Aahil78/KB75/src/KB75.kicad_sch

## KiCad design src/KB75.kicad_sch (2025-06-21, an earlier design)

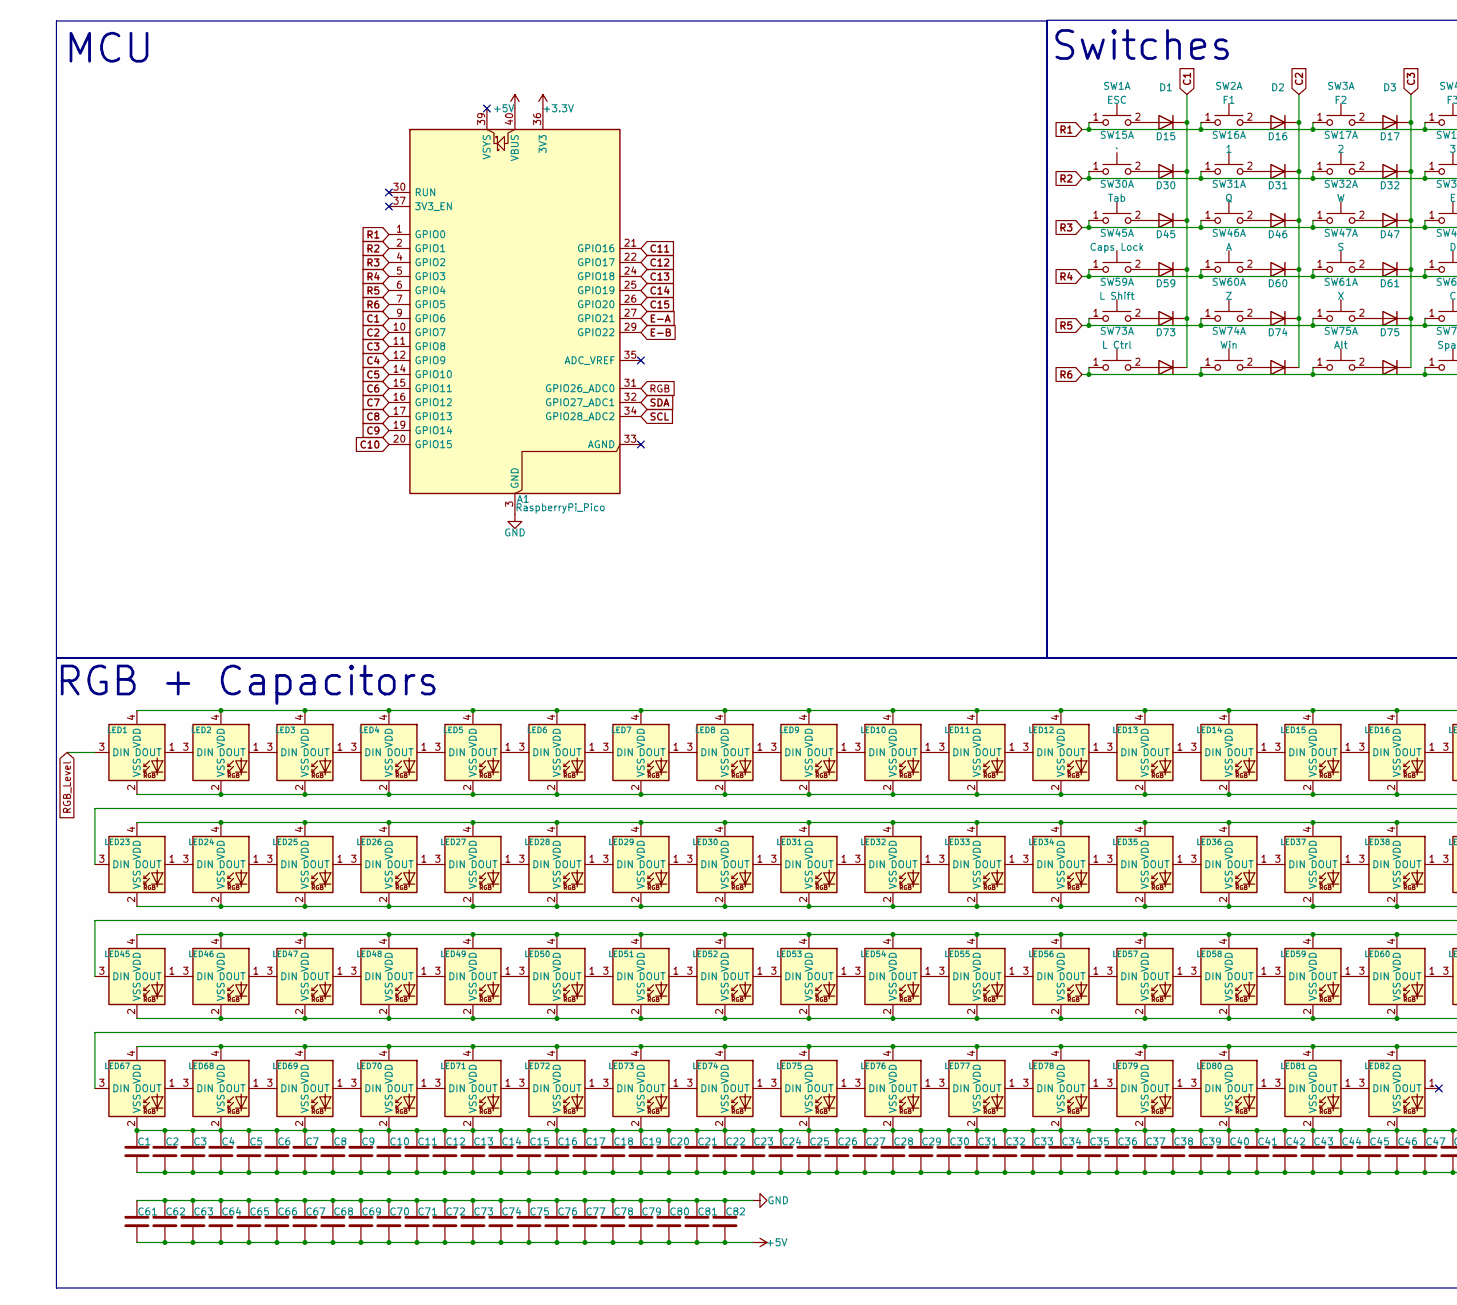
[picture p9: schematic KB75.kicad_sch, part in row 1, column 1]

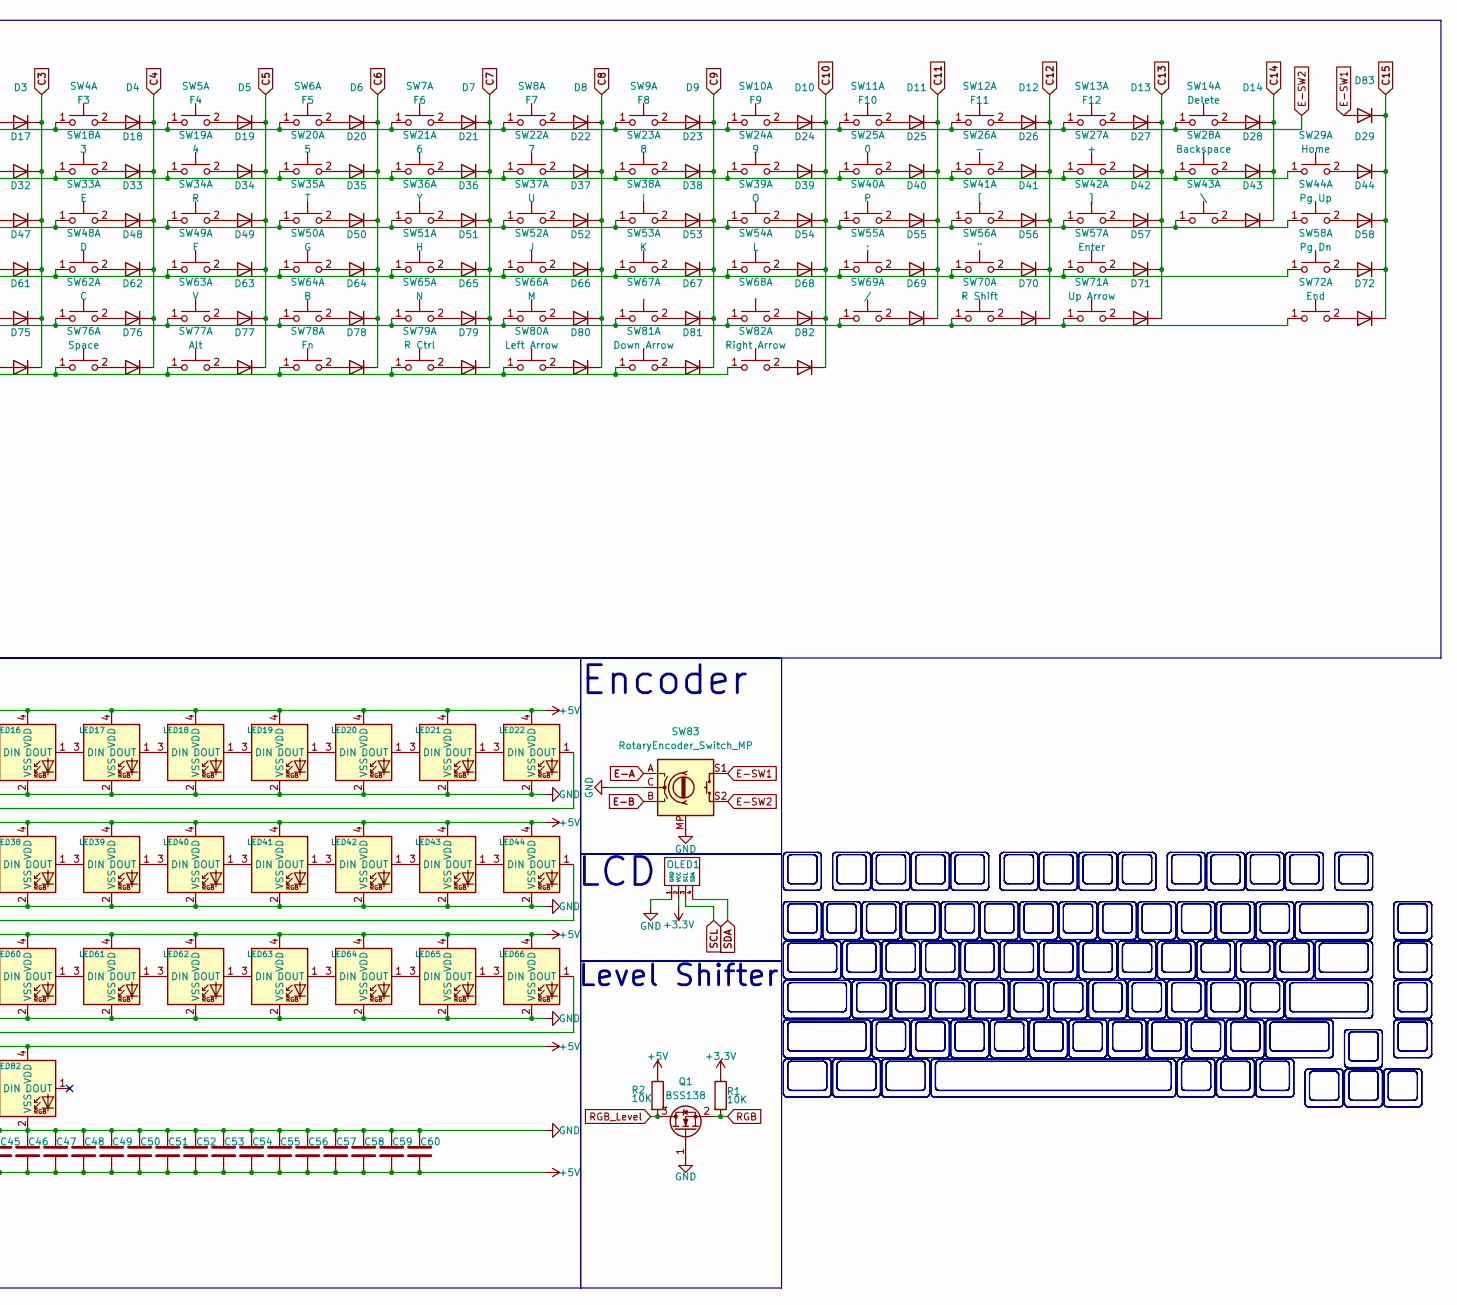
[picture p10: schematic KB75.kicad_sch, part in row 1, column 2]

Parts:
A1: RaspberryPi_Pico; RaspberryPi_Pico_Common_Unspecified
C1, C2, C3, C4, C5, C6, C7, C8, C9, C10, C11, C12, C13, C14, C15, C16, C17, C18, C19, C20, C21, C22, C23, C24, C25, C26, C27, C28, C29, C30, C31, C32, C33, C34, C35, C36, C37, C38, C39, C40, C41, C42, C43, C44, C45, C46, C47, C48, C49, C50, C51, C52, C53, C54, C55, C56, C57, C58, C59, C60, C61, C62, C63, C64, C65, C66, C67, C68, C69, C70, C71, C72, C73, C74, C75, C76, C77, C78, C79, C80, C81, C82: C; C_0805_2012Metric_Pad1.18x1.45mm_HandSolder
D1, D2, D3, D4, D5, D6, D7, D8, D9, D10, D11, D12, D13, D14, D15, D16, D17, D18, D19, D20, D21, D22, D23, D24, D25, D26, D27, D28, D29, D30, D31, D32, D33, D34, D35, D36, D37, D38, D39, D40, D41, D42, D43, D44, D45, D46, D47, D48, D49, D50, D51, D52, D53, D54, D55, D56, D57, D58, D59, D60, D61, D62, D63, D64, D65, D66, D67, D68, D69, D70, D71, D72, D73, D74, D75, D76, D77, D78, D79, D80, D81, D82, D83: D; D_0805_2012Metric_Pad1.15x1.40mm_HandSolder
LED1, LED2, LED3, LED4, LED5, LED6, LED7, LED8, LED9, LED10, LED11, LED12, LED13, LED14, LED15, LED16, LED17, LED18, LED19, LED20, LED21, LED22, LED23, LED24, LED25, LED26, LED27, LED28, LED29, LED30, LED31, LED32, LED33, LED34, LED35, LED36, LED37, LED38, LED39, LED40, LED41, LED42, LED43, LED44, LED45, LED46, LED47, LED48, LED49, LED50, LED51, LED52, LED53, LED54, LED55, LED56, LED57, LED58, LED59, LED60, LED61, LED62, LED63, LED64, LED65, LED66, LED67, LED68, LED69, LED70, LED71, LED72, LED73, LED74, LED75, LED76, LED77, LED78, LED79, LED80, LED81, LED82: MX_SK6812MINI-E
OLED1: SSD1306-0.91-OLED-4pin-128x32
Q1: BSS138; SOT-23
R1, R2: 10K; R_0805_2012Metric_Pad1.20x1.40mm_HandSolder
SW1: ESC; SW_Hotswap_Kailh_MX_1.00u
SW2: F1; SW_Hotswap_Kailh_MX_1.00u
SW3: F2; SW_Hotswap_Kailh_MX_1.00u
SW4: F3; SW_Hotswap_Kailh_MX_1.00u
SW5: F4; SW_Hotswap_Kailh_MX_1.00u
SW6: F5; SW_Hotswap_Kailh_MX_1.00u
SW7: F6; SW_Hotswap_Kailh_MX_1.00u
SW8: F7; SW_Hotswap_Kailh_MX_1.00u
SW9: F8; SW_Hotswap_Kailh_MX_1.00u
SW10: F9; SW_Hotswap_Kailh_MX_1.00u
SW11: F10; SW_Hotswap_Kailh_MX_1.00u
SW12: F11; SW_Hotswap_Kailh_MX_1.00u
SW13: F12; SW_Hotswap_Kailh_MX_1.00u
SW14: Delete; SW_Hotswap_Kailh_MX_1.00u
SW15: `; SW_Hotswap_Kailh_MX_1.00u
SW16: 1; SW_Hotswap_Kailh_MX_1.00u
SW17: 2; SW_Hotswap_Kailh_MX_1.00u
SW18: 3; SW_Hotswap_Kailh_MX_1.00u
SW19: 4; SW_Hotswap_Kailh_MX_1.00u
SW20: 5; SW_Hotswap_Kailh_MX_1.00u
SW21: 6; SW_Hotswap_Kailh_MX_1.00u
SW22: 7; SW_Hotswap_Kailh_MX_1.00u
SW23: 8; SW_Hotswap_Kailh_MX_1.00u
SW24: 9; SW_Hotswap_Kailh_MX_1.00u
SW25: 0; SW_Hotswap_Kailh_MX_1.00u
SW26: -; SW_Hotswap_Kailh_MX_1.00u
SW27: +; SW_Hotswap_Kailh_MX_1.00u
SW28: Backspace; SW_Hotswap_Kailh_MX_1.00u
SW29: Home; SW_Hotswap_Kailh_MX_1.00u
SW30: Tab; SW_Hotswap_Kailh_MX_1.00u
SW31: Q; SW_Hotswap_Kailh_MX_1.00u
SW32: W; SW_Hotswap_Kailh_MX_1.00u
SW33: E; SW_Hotswap_Kailh_MX_1.00u
SW34: R; SW_Hotswap_Kailh_MX_1.00u
SW35: T; SW_Hotswap_Kailh_MX_1.00u
SW36: Y; SW_Hotswap_Kailh_MX_1.00u
SW37: U; SW_Hotswap_Kailh_MX_1.00u
SW38: I; SW_Hotswap_Kailh_MX_1.00u
SW39: O; SW_Hotswap_Kailh_MX_1.00u
SW40: P; SW_Hotswap_Kailh_MX_1.00u
SW41: [; SW_Hotswap_Kailh_MX_1.00u
SW42: ]; SW_Hotswap_Kailh_MX_1.00u
SW43: \; SW_Hotswap_Kailh_MX_1.00u
SW44: Pg Up; SW_Hotswap_Kailh_MX_1.00u
SW45: Caps Lock; SW_Hotswap_Kailh_MX_1.00u
SW46: A; SW_Hotswap_Kailh_MX_1.00u
SW47: S; SW_Hotswap_Kailh_MX_1.00u
SW48: D; SW_Hotswap_Kailh_MX_1.00u
SW49: F; SW_Hotswap_Kailh_MX_1.00u
SW50: G; SW_Hotswap_Kailh_MX_1.00u
SW51: H; SW_Hotswap_Kailh_MX_1.00u
SW52: J; SW_Hotswap_Kailh_MX_1.00u
SW53: K; SW_Hotswap_Kailh_MX_1.00u
SW54: L; SW_Hotswap_Kailh_MX_1.00u
SW55: ;; SW_Hotswap_Kailh_MX_1.00u
SW56: "; SW_Hotswap_Kailh_MX_1.00u
SW57: Enter; SW_Hotswap_Kailh_MX_1.00u
SW58: Pg Dn; SW_Hotswap_Kailh_MX_1.00u
SW59: L Shift; SW_Hotswap_Kailh_MX_1.00u
SW60: Z; SW_Hotswap_Kailh_MX_1.00u
SW61: X; SW_Hotswap_Kailh_MX_1.00u
SW62: C; SW_Hotswap_Kailh_MX_1.00u
SW63: V; SW_Hotswap_Kailh_MX_1.00u
SW64: B; SW_Hotswap_Kailh_MX_1.00u
SW65: N; SW_Hotswap_Kailh_MX_1.00u
SW66: M; SW_Hotswap_Kailh_MX_1.00u
SW67: ,; SW_Hotswap_Kailh_MX_1.00u
SW68: .; SW_Hotswap_Kailh_MX_1.00u
SW69: /; SW_Hotswap_Kailh_MX_1.00u
SW70: R Shift; SW_Hotswap_Kailh_MX_1.00u
SW71: Up Arrow; SW_Hotswap_Kailh_MX_1.00u
SW72: End; SW_Hotswap_Kailh_MX_1.00u
SW73: L Ctrl; SW_Hotswap_Kailh_MX_1.00u
SW74: Win; SW_Hotswap_Kailh_MX_1.00u
SW75, SW77: Alt; SW_Hotswap_Kailh_MX_1.00u
SW76: Space; SW_Hotswap_Kailh_MX_1.00u
SW78: Fn; SW_Hotswap_Kailh_MX_1.00u
SW79: R Ctrl; SW_Hotswap_Kailh_MX_1.00u
SW80: Left Arrow; SW_Hotswap_Kailh_MX_1.00u
SW81: Down Arrow; SW_Hotswap_Kailh_MX_1.00u
SW82: Right Arrow; SW_Hotswap_Kailh_MX_1.00u
SW83: RotaryEncoder_Switch_MP; RotaryEncoder_Alps_EC11E-Switch_Vertical_H20mm

Connections:
+3.3V: A1.36 (3V3), OLED1.2 (VCC), R1.1
+5V: A1.40 (VBUS), C1.2, C2.2, C3.2, C4.2, C5.2, C6.2, C7.2, C8.2, C9.2, C10.2, C11.2, C12.2, C13.2, C14.2, C15.2, C16.2, C17.2, C18.2, C19.2, C20.2, C21.2, C22.2, C23.2, C24.2, C25.2, C26.2, C27.2, C28.2, C29.2, C30.2, C31.2, C32.2, C33.2, C34.2, C35.2, C36.2, C37.2, C38.2, C39.2, C40.2, C41.2, C42.2, C43.2, C44.2, C45.2, C46.2, C47.2, C48.2, C49.2, C50.2, C51.2, C52.2, C53.2, C54.2, C55.2, C56.2, C57.2, C58.2, C59.2, C60.2, C61.2, C62.2, C63.2, C64.2, C65.2, C66.2, C67.2, C68.2, C69.2, C70.2, C71.2, C72.2, C73.2, C74.2, C75.2, C76.2, C77.2, C78.2, C79.2, C80.2, C81.2, C82.2, LED1.4 (VDD), LED2.4 (VDD), LED3.4 (VDD), LED4.4 (VDD), LED5.4 (VDD), LED6.4 (VDD), LED7.4 (VDD), LED8.4 (VDD), LED9.4 (VDD), LED10.4 (VDD), LED11.4 (VDD), LED12.4 (VDD), LED13.4 (VDD), LED14.4 (VDD), LED15.4 (VDD), LED16.4 (VDD), LED17.4 (VDD), LED18.4 (VDD), LED19.4 (VDD), LED20.4 (VDD), LED21.4 (VDD), LED22.4 (VDD), LED23.4 (VDD), LED24.4 (VDD), LED25.4 (VDD), LED26.4 (VDD), LED27.4 (VDD), LED28.4 (VDD), LED29.4 (VDD), LED30.4 (VDD), LED31.4 (VDD), LED32.4 (VDD), LED33.4 (VDD), LED34.4 (VDD), LED35.4 (VDD), LED36.4 (VDD), LED37.4 (VDD), LED38.4 (VDD), LED39.4 (VDD), LED40.4 (VDD), LED41.4 (VDD), LED42.4 (VDD), LED43.4 (VDD), LED44.4 (VDD), LED45.4 (VDD), LED46.4 (VDD), LED47.4 (VDD), LED48.4 (VDD), LED49.4 (VDD), LED50.4 (VDD), LED51.4 (VDD), LED52.4 (VDD), LED53.4 (VDD), LED54.4 (VDD), LED55.4 (VDD), LED56.4 (VDD), LED57.4 (VDD), LED58.4 (VDD), LED59.4 (VDD), LED60.4 (VDD), LED61.4 (VDD), LED62.4 (VDD), LED63.4 (VDD), LED64.4 (VDD), LED65.4 (VDD), LED66.4 (VDD), LED67.4 (VDD), LED68.4 (VDD), LED69.4 (VDD), LED70.4 (VDD), LED71.4 (VDD), LED72.4 (VDD), LED73.4 (VDD), LED74.4 (VDD), LED75.4 (VDD), LED76.4 (VDD), LED77.4 (VDD), LED78.4 (VDD), LED79.4 (VDD), LED80.4 (VDD), LED81.4 (VDD), LED82.4 (VDD), R2.1
C1: A1.9 (GPIO6), D1.1 (K), D15.1 (K), D30.1 (K), D45.1 (K), D59.1 (K), D73.1 (K)
C2: A1.10 (GPIO7), D2.1 (K), D16.1 (K), D31.1 (K), D46.1 (K), D60.1 (K), D74.1 (K)
C3: A1.11 (GPIO8), D3.1 (K), D17.1 (K), D32.1 (K), D47.1 (K), D61.1 (K), D75.1 (K)
C4: A1.12 (GPIO9), D4.1 (K), D18.1 (K), D33.1 (K), D48.1 (K), D62.1 (K), D76.1 (K)
C5: A1.14 (GPIO10), D5.1 (K), D19.1 (K), D34.1 (K), D49.1 (K), D63.1 (K), D77.1 (K)
C6: A1.15 (GPIO11), D6.1 (K), D20.1 (K), D35.1 (K), D50.1 (K), D64.1 (K), D78.1 (K)
C7: A1.16 (GPIO12), D7.1 (K), D21.1 (K), D36.1 (K), D51.1 (K), D65.1 (K), D79.1 (K)
C8: A1.17 (GPIO13), D8.1 (K), D22.1 (K), D37.1 (K), D52.1 (K), D66.1 (K), D80.1 (K)
C9: A1.19 (GPIO14), D9.1 (K), D23.1 (K), D38.1 (K), D53.1 (K), D67.1 (K), D81.1 (K)
C10: A1.20 (GPIO15), D10.1 (K), D24.1 (K), D39.1 (K), D54.1 (K), D68.1 (K), D82.1 (K)
C11: A1.21 (GPIO16), D11.1 (K), D25.1 (K), D40.1 (K), D55.1 (K), D69.1 (K)
C12: A1.22 (GPIO17), D12.1 (K), D26.1 (K), D41.1 (K), D56.1 (K), D70.1 (K)
C13: A1.24 (GPIO18), D13.1 (K), D27.1 (K), D42.1 (K), D57.1 (K), D71.1 (K)
C14: A1.25 (GPIO19), D14.1 (K), D28.1 (K), D43.1 (K)
C15: A1.26 (GPIO20), D29.1 (K), D44.1 (K), D58.1 (K), D72.1 (K), D83.1 (K)
E-A: A1.27 (GPIO21), SW83.A
E-B: A1.29 (GPIO22), SW83.B
E-SW1: D83.2 (A), SW83.S1
E-SW2: A1.1 (GPIO0), SW1.1, SW2.1, SW3.1, SW4.1, SW5.1, SW6.1, SW7.1, SW8.1, SW9.1, SW10.1, SW11.1, SW12.1, SW13.1, SW14.1, SW83.S2
GND: A1.3 (GND), A1.8 (GND), A1.13 (GND), A1.18 (GND), A1.23 (GND), A1.28 (GND), A1.38 (GND), C1.1, C2.1, C3.1, C4.1, C5.1, C6.1, C7.1, C8.1, C9.1, C10.1, C11.1, C12.1, C13.1, C14.1, C15.1, C16.1, C17.1, C18.1, C19.1, C20.1, C21.1, C22.1, C23.1, C24.1, C25.1, C26.1, C27.1, C28.1, C29.1, C30.1, C31.1, C32.1, C33.1, C34.1, C35.1, C36.1, C37.1, C38.1, C39.1, C40.1, C41.1, C42.1, C43.1, C44.1, C45.1, C46.1, C47.1, C48.1, C49.1, C50.1, C51.1, C52.1, C53.1, C54.1, C55.1, C56.1, C57.1, C58.1, C59.1, C60.1, C61.1, C62.1, C63.1, C64.1, C65.1, C66.1, C67.1, C68.1, C69.1, C70.1, C71.1, C72.1, C73.1, C74.1, C75.1, C76.1, C77.1, C78.1, C79.1, C80.1, C81.1, C82.1, LED1.2 (VSS), LED2.2 (VSS), LED3.2 (VSS), LED4.2 (VSS), LED5.2 (VSS), LED6.2 (VSS), LED7.2 (VSS), LED8.2 (VSS), LED9.2 (VSS), LED10.2 (VSS), LED11.2 (VSS), LED12.2 (VSS), LED13.2 (VSS), LED14.2 (VSS), LED15.2 (VSS), LED16.2 (VSS), LED17.2 (VSS), LED18.2 (VSS), LED19.2 (VSS), LED20.2 (VSS), LED21.2 (VSS), LED22.2 (VSS), LED23.2 (VSS), LED24.2 (VSS), LED25.2 (VSS), LED26.2 (VSS), LED27.2 (VSS), LED28.2 (VSS), LED29.2 (VSS), LED30.2 (VSS), LED31.2 (VSS), LED32.2 (VSS), LED33.2 (VSS), LED34.2 (VSS), LED35.2 (VSS), LED36.2 (VSS), LED37.2 (VSS), LED38.2 (VSS), LED39.2 (VSS), LED40.2 (VSS), LED41.2 (VSS), LED42.2 (VSS), LED43.2 (VSS), LED44.2 (VSS), LED45.2 (VSS), LED46.2 (VSS), LED47.2 (VSS), LED48.2 (VSS), LED49.2 (VSS), LED50.2 (VSS), LED51.2 (VSS), LED52.2 (VSS), LED53.2 (VSS), LED54.2 (VSS), LED55.2 (VSS), LED56.2 (VSS), LED57.2 (VSS), LED58.2 (VSS), LED59.2 (VSS), LED60.2 (VSS), LED61.2 (VSS), LED62.2 (VSS), LED63.2 (VSS), LED64.2 (VSS), LED65.2 (VSS), LED66.2 (VSS), LED67.2 (VSS), LED68.2 (VSS), LED69.2 (VSS), LED70.2 (VSS), LED71.2 (VSS), LED72.2 (VSS), LED73.2 (VSS), LED74.2 (VSS), LED75.2 (VSS), LED76.2 (VSS), LED77.2 (VSS), LED78.2 (VSS), LED79.2 (VSS), LED80.2 (VSS), LED81.2 (VSS), LED82.2 (VSS), OLED1.1 (GND), Q1.1 (G), SW83.C, SW83.MP
unnamed: D1.2 (A), SW1.2
unnamed: D2.2 (A), SW2.2
unnamed: D3.2 (A), SW3.2
unnamed: D4.2 (A), SW4.2
unnamed: D5.2 (A), SW5.2
unnamed: D6.2 (A), SW6.2
unnamed: D7.2 (A), SW7.2
unnamed: D8.2 (A), SW8.2
unnamed: D9.2 (A), SW9.2
unnamed: D10.2 (A), SW10.2
unnamed: D11.2 (A), SW11.2
unnamed: D12.2 (A), SW12.2
unnamed: D13.2 (A), SW13.2
unnamed: D14.2 (A), SW14.2
unnamed: D15.2 (A), SW15.2
unnamed: D16.2 (A), SW16.2
unnamed: D17.2 (A), SW17.2
unnamed: D18.2 (A), SW18.2
unnamed: D19.2 (A), SW19.2
unnamed: D20.2 (A), SW20.2
unnamed: D21.2 (A), SW21.2
unnamed: D22.2 (A), SW22.2
unnamed: D23.2 (A), SW23.2
unnamed: D24.2 (A), SW24.2
unnamed: D25.2 (A), SW25.2
unnamed: D26.2 (A), SW26.2
unnamed: D27.2 (A), SW27.2
unnamed: D28.2 (A), SW28.2
unnamed: D29.2 (A), SW29.2
unnamed: D30.2 (A), SW30.2
unnamed: D31.2 (A), SW31.2
unnamed: D32.2 (A), SW32.2
unnamed: D33.2 (A), SW33.2
unnamed: D34.2 (A), SW34.2
unnamed: D35.2 (A), SW35.2
unnamed: D36.2 (A), SW36.2
unnamed: D37.2 (A), SW37.2
unnamed: D38.2 (A), SW38.2
unnamed: D39.2 (A), SW39.2
unnamed: D40.2 (A), SW40.2
unnamed: D41.2 (A), SW41.2
unnamed: D42.2 (A), SW42.2
unnamed: D43.2 (A), SW43.2
unnamed: D44.2 (A), SW44.2
unnamed: D45.2 (A), SW45.2
unnamed: D46.2 (A), SW46.2
unnamed: D47.2 (A), SW47.2
unnamed: D48.2 (A), SW48.2
unnamed: D49.2 (A), SW49.2
unnamed: D50.2 (A), SW50.2
unnamed: D51.2 (A), SW51.2
unnamed: D52.2 (A), SW52.2
unnamed: D53.2 (A), SW53.2
unnamed: D54.2 (A), SW54.2
unnamed: D55.2 (A), SW55.2
unnamed: D56.2 (A), SW56.2
unnamed: D57.2 (A), SW57.2
unnamed: D58.2 (A), SW58.2
unnamed: D59.2 (A), SW59.2
unnamed: D60.2 (A), SW60.2
unnamed: D61.2 (A), SW61.2
unnamed: D62.2 (A), SW62.2
unnamed: D63.2 (A), SW63.2
unnamed: D64.2 (A), SW64.2
unnamed: D65.2 (A), SW65.2
unnamed: D66.2 (A), SW66.2
unnamed: D67.2 (A), SW67.2
unnamed: D68.2 (A), SW68.2
unnamed: D69.2 (A), SW69.2
unnamed: D70.2 (A), SW70.2
unnamed: D71.2 (A), SW71.2
unnamed: D72.2 (A), SW72.2
unnamed: D73.2 (A), SW73.2
unnamed: D74.2 (A), SW74.2
unnamed: D75.2 (A), SW75.2
unnamed: D76.2 (A), SW76.2
unnamed: D77.2 (A), SW77.2
unnamed: D78.2 (A), SW78.2
unnamed: D79.2 (A), SW79.2
unnamed: D80.2 (A), SW80.2
unnamed: D81.2 (A), SW81.2
unnamed: D82.2 (A), SW82.2
unnamed: LED1.1 (DOUT), LED2.3 (DIN)
unnamed: LED2.1 (DOUT), LED3.3 (DIN)
unnamed: LED3.1 (DOUT), LED4.3 (DIN)
unnamed: LED4.1 (DOUT), LED5.3 (DIN)
unnamed: LED5.1 (DOUT), LED6.3 (DIN)
unnamed: LED6.1 (DOUT), LED7.3 (DIN)
unnamed: LED7.1 (DOUT), LED8.3 (DIN)
unnamed: LED8.1 (DOUT), LED9.3 (DIN)
unnamed: LED10.1 (DOUT), LED11.3 (DIN)
unnamed: LED9.1 (DOUT), LED10.3 (DIN)
unnamed: LED11.1 (DOUT), LED12.3 (DIN)
unnamed: LED12.1 (DOUT), LED13.3 (DIN)
unnamed: LED13.1 (DOUT), LED14.3 (DIN)
unnamed: LED14.1 (DOUT), LED15.3 (DIN)
unnamed: LED15.1 (DOUT), LED16.3 (DIN)
unnamed: LED16.1 (DOUT), LED17.3 (DIN)
unnamed: LED17.1 (DOUT), LED18.3 (DIN)
unnamed: LED18.1 (DOUT), LED19.3 (DIN)
unnamed: LED19.1 (DOUT), LED20.3 (DIN)
unnamed: LED20.1 (DOUT), LED21.3 (DIN)
unnamed: LED21.1 (DOUT), LED22.3 (DIN)
unnamed: LED22.1 (DOUT), LED23.3 (DIN)
unnamed: LED23.1 (DOUT), LED24.3 (DIN)
unnamed: LED24.1 (DOUT), LED25.3 (DIN)
unnamed: LED25.1 (DOUT), LED26.3 (DIN)
unnamed: LED26.1 (DOUT), LED27.3 (DIN)
unnamed: LED27.1 (DOUT), LED28.3 (DIN)
unnamed: LED28.1 (DOUT), LED29.3 (DIN)
unnamed: LED29.1 (DOUT), LED30.3 (DIN)
unnamed: LED30.1 (DOUT), LED31.3 (DIN)
unnamed: LED31.1 (DOUT), LED32.3 (DIN)
unnamed: LED32.1 (DOUT), LED33.3 (DIN)
unnamed: LED33.1 (DOUT), LED34.3 (DIN)
unnamed: LED34.1 (DOUT), LED35.3 (DIN)
unnamed: LED35.1 (DOUT), LED36.3 (DIN)
unnamed: LED36.1 (DOUT), LED37.3 (DIN)
unnamed: LED37.1 (DOUT), LED38.3 (DIN)
unnamed: LED38.1 (DOUT), LED39.3 (DIN)
unnamed: LED39.1 (DOUT), LED40.3 (DIN)
unnamed: LED40.1 (DOUT), LED41.3 (DIN)
unnamed: LED41.1 (DOUT), LED42.3 (DIN)
unnamed: LED42.1 (DOUT), LED43.3 (DIN)
unnamed: LED43.1 (DOUT), LED44.3 (DIN)
unnamed: LED44.1 (DOUT), LED45.3 (DIN)
unnamed: LED45.1 (DOUT), LED46.3 (DIN)
unnamed: LED46.1 (DOUT), LED47.3 (DIN)
unnamed: LED47.1 (DOUT), LED48.3 (DIN)
unnamed: LED48.1 (DOUT), LED49.3 (DIN)
unnamed: LED49.1 (DOUT), LED50.3 (DIN)
unnamed: LED50.1 (DOUT), LED51.3 (DIN)
unnamed: LED51.1 (DOUT), LED52.3 (DIN)
unnamed: LED52.1 (DOUT), LED53.3 (DIN)
unnamed: LED53.1 (DOUT), LED54.3 (DIN)
unnamed: LED54.1 (DOUT), LED55.3 (DIN)
unnamed: LED55.1 (DOUT), LED56.3 (DIN)
unnamed: LED56.1 (DOUT), LED57.3 (DIN)
unnamed: LED57.1 (DOUT), LED58.3 (DIN)
unnamed: LED58.1 (DOUT), LED59.3 (DIN)
unnamed: LED59.1 (DOUT), LED60.3 (DIN)
unnamed: LED60.1 (DOUT), LED61.3 (DIN)
unnamed: LED61.1 (DOUT), LED62.3 (DIN)
unnamed: LED62.1 (DOUT), LED63.3 (DIN)
unnamed: LED63.1 (DOUT), LED64.3 (DIN)
unnamed: LED64.1 (DOUT), LED65.3 (DIN)
unnamed: LED65.1 (DOUT), LED66.3 (DIN)
unnamed: LED66.1 (DOUT), LED67.3 (DIN)
unnamed: LED67.1 (DOUT), LED68.3 (DIN)
unnamed: LED68.1 (DOUT), LED69.3 (DIN)
unnamed: LED69.1 (DOUT), LED70.3 (DIN)
unnamed: LED70.1 (DOUT), LED71.3 (DIN)
unnamed: LED71.1 (DOUT), LED72.3 (DIN)
unnamed: LED72.1 (DOUT), LED73.3 (DIN)
unnamed: LED73.1 (DOUT), LED74.3 (DIN)
unnamed: LED74.1 (DOUT), LED75.3 (DIN)
unnamed: LED75.1 (DOUT), LED76.3 (DIN)
unnamed: LED76.1 (DOUT), LED77.3 (DIN)
unnamed: LED77.1 (DOUT), LED78.3 (DIN)
unnamed: LED78.1 (DOUT), LED79.3 (DIN)
unnamed: LED79.1 (DOUT), LED80.3 (DIN)
unnamed: LED80.1 (DOUT), LED81.3 (DIN)
unnamed: LED81.1 (DOUT), LED82.3 (DIN)
R2: A1.2 (GPIO1), SW15.1, SW16.1, SW17.1, SW18.1, SW19.1, SW20.1, SW21.1, SW22.1, SW23.1, SW24.1, SW25.1, SW26.1, SW27.1, SW28.1, SW29.1
R3: A1.4 (GPIO2), SW30.1, SW31.1, SW32.1, SW33.1, SW34.1, SW35.1, SW36.1, SW37.1, SW38.1, SW39.1, SW40.1, SW41.1, SW42.1, SW43.1, SW44.1
R4: A1.5 (GPIO3), SW45.1, SW46.1, SW47.1, SW48.1, SW49.1, SW50.1, SW51.1, SW52.1, SW53.1, SW54.1, SW55.1, SW56.1, SW57.1, SW58.1
R5: A1.6 (GPIO4), SW59.1, SW60.1, SW61.1, SW62.1, SW63.1, SW64.1, SW65.1, SW66.1, SW67.1, SW68.1, SW69.1, SW70.1, SW71.1, SW72.1
R6: A1.7 (GPIO5), SW73.1, SW74.1, SW75.1, SW76.1, SW77.1, SW78.1, SW79.1, SW80.1, SW81.1, SW82.1
RGB: A1.31 (GPIO26_ADC0), Q1.2 (S), R1.2
RGB_Level: LED1.3 (DIN), Q1.3 (D), R2.2
SCL: A1.34 (GPIO28_ADC2), OLED1.3 (SCL)
SDA: A1.32 (GPIO27_ADC1), OLED1.4 (SDA)

Notes on the sheet:
RGB + Capacitors
Switches
MCU
LCD
Level Shifter
Encoder
